tommyy94/Exploring-KL25/Remote/Src/comm.c

#include "comm.h"


/* Local defines */

/* Global variables */
QueueHandle_t xCommQueue;
SemaphoreHandle_t xCommSemaphore;
TaskHandle_t xCommTask = NULL;

struct AMessage
{
    char ucFrame[MAX_FRAME_SIZE];
} xMessage;

    
/* Function descriptions */

/**
 * @brief   FreeRTOS communication task.
 * 
 * @param   pvParam     Unused.
 * 
 * @return  None
 */
void vCommTask(void *const pvParam)
{
    (void)pvParam;
    BaseType_t xAssert;
    struct AMessage *pxMessage;
    const TickType_t xTicksToWait = 100 / portTICK_PERIOD_MS;
    
    for (;;)
    {
        if (xQueueReceive(xCommQueue, &(pxMessage), (TickType_t) 10))
        {
            /* Guard nRF24L01 */
            if (xSemaphoreTake(xCommSemaphore, (TickType_t)xTicksToWait))
            {
                nRF24L01_vSendPayload(pxMessage->ucFrame, strlen(pxMessage->ucFrame));

                /* This call should not fail in any circumstance */
                xAssert = xSemaphoreGive(xCommSemaphore);
                configASSERT(xAssert == pdTRUE);
            }
        }
        
        vTaskDelay(pdMS_TO_TICKS(50));
    }
}


/**
 * @brief   FreeRTOS frame task. Builds the message to send.
 * 
 * @param   pvParam     Unused.
 * 
 * @return  None
 */
void vFrameTask(void *const pvParam)
{
    (void)pvParam;
    int32_t lBytesWritten;
    BaseType_t xAssert;
    
    struct Sensor *pxSensor;
    struct AMessage *pxMessage;
    pxMessage = &xMessage;
    
    for (;;)
    {
        if (xAnalogQueue != 0)
        {
            if (xQueueReceive(xAnalogQueue, &pxSensor, (TickType_t)50))
            {
                /* Build the frame */
                lBytesWritten = csnprintf(pxMessage->ucFrame, MAX_FRAME_SIZE, "tmp=%ldhum=%lumst=%lu", pxSensor->lTemperature, pxSensor->ulHumidity, pxSensor->ulSoilMoisture);
                configASSERT(lBytesWritten >= 0);
            
                /* Transmit */
                xAssert = xQueueSend(xCommQueue, (void *)&pxMessage, (TickType_t)10);
                configASSERT(xAssert);
            }
        }
        
        vTaskDelay(pdMS_TO_TICKS(100));
    }
}


/**
 * @brief   Sets SPI1 SS line high and stops DMA0.
 * 
 * @param   None
 * 
 * @return  None
 */
void TPM2_IRQHandler(void)
{
    BaseType_t xHigherPriorityTaskWoken = pdFALSE;
    
    if (BME_UBFX32(&TPM2->STATUS, TPM_STATUS_TOF_SHIFT, TPM_STATUS_TOF_WIDTH))
    {
        /* Cleanup */
        SPI1_vSetSlave(HIGH);
        TPM2_vStop();

        /* Should not be NULL as transmission was in progress */
        configASSERT(xCommTask != NULL);

        /* Notify task */
        vTaskNotifyGiveFromISR(xCommTask, &xHigherPriorityTaskWoken);
        
        /* Transmission no longer in progress */
        xCommTask = NULL;
    }

    /* Clear Timer Overflow Flag */
    BME_OR32(&TPM2->STATUS, TPM_STATUS_TOF(1));

    /* Force context switch if xHigherPriorityTaskWoken is set pdTRUE */
    portEND_SWITCHING_ISR(xHigherPriorityTaskWoken);
}
