tommyy94/Exploring-KL25/Remote/Inc/includes.h

#pragma once

#include <stdlib.h>
#include <string.h>

#include "MKL25Z4.h"

#include "defines.h"
#include "printf-stdarg.h"
#include "system.h"
#include "motor.h"
#include "comm.h"
#include "sensors.h"
#include "adc.h"
#include "dma.h"
#include "tpm.h"
#include "spi.h"
#include "HS1101.h"
#include "nrf24l01.h"
