tommyy94/Exploring-KL25/Remote/Src/HS1101.c

/* User headers */
#include  "HS1101.h"

/* Local defines */
#define HUMIDITY_FORMULA(x) ((x))

/* Local variables */
TaskHandle_t xAnalogNotification = NULL;

/* Local function prototypes */
static void HS1101_vSendSignal(void);


/* Function descriptions */

/**
 * @brief   This function simply sets ports output & writes high to memory so
 *          multiplexing pins sets pin high.
 * 
 * @param   None
 * 
 * @return  None
 */
void HS1101_vInit(void)
{
    FGPIOE->PDDR |= MASK(HUMID_SENSOR_PIN);
    FGPIOE->PSOR |= MASK(HUMID_SENSOR_PIN);
}


/**
 * @brief   Start measuring HS1101 capacitance using CMP0 and TPM0 Input Capture mode.
 *          This function disables context switches for few cycles, because timer and
 *          comparator must be started at the same time.
 * 
 * @param   None
 * 
 * @return  None
 */
static void HS1101_vSendSignal(void)
{    
    /* Charge capacitor */
    BME_OR32(&PORTE->PCR[HUMID_SENSOR_PIN], PORT_PCR_MUX(ALT1));
    
    /* Start atomic operations */
    taskENTER_CRITICAL();
    
    /* Start timer */
    BME_OR32(&TPM1->SC, TPM_SC_CMOD(1));
    
    /* Set IO to inverted comparator mode */
    BME_BFI32(&PORTE->PCR[HUMID_SENSOR_PIN], ALT0 << PORT_PCR_MUX_SHIFT, PORT_PCR_MUX_SHIFT, 1);
    
    /* Stop atomic operations */
    taskEXIT_CRITICAL();
}


/**
 * @brief   Read variable capacitor HS1101 using CMP0 and TMP0.
 * 
 * @param   None
 * 
 * @return  ulHumid     Air humidity value.
 * 
 * @todo    Calibrate humidity sensor
 */
uint32_t HS1101_ulReadHumidity(void)
{
    BaseType_t xAssert;
    const TickType_t xTicksToWait = 100 / portTICK_PERIOD_MS;
    uint32_t HS1101_ulValue = 0;
    uint32_t ulHumid = 0;
    
    /* No conversion should be in progress */
    configASSERT(xAnalogNotification == NULL);
    
    /* Update status */
    xAnalogNotification = xTaskGetCurrentTaskHandle();
    
    /* Start conversion */
    HS1101_vSendSignal();
    
    /* Wait until conversion done */
    xAssert = xTaskNotifyWait(0x00, 0xFFFFFFFF, &HS1101_ulValue, xTicksToWait);
    configASSERT(xAssert == pdPASS);
    
    /* Convert analog value and return it */
    ulHumid = HUMIDITY_FORMULA(HS1101_ulValue);
    return (ulHumid);
}
