tommyy94/Exploring-KL25/kl25_test/Src/gpio.c

#include "gpio.h"


/* Function descriptions */

/**
 * @brief   Mainly used for debugging purposes.
 * 
 * @param   None
 * 
 * @return  None
 */
void GPIO_vInit(void)
{
    /* Enable clock to PORTD */
    SIM->SCGC5 |= SIM_SCGC5_PORTD_MASK;
    
    /* Select GPIO for pin */
    PORTD->PCR[SIGNAL_SHIFT] = PORT_PCR_MUX(ALT1);
    
    /* Set port to output */
    FGPIOD->PDDR |= MASK(SIGNAL_SHIFT);
}
