tommyy94/Exploring-KL25/kl25_test/Inc/gpio.h

/**
 * gpioh.
 * This compilation unit handles GPIO.
 */

#pragma once

/* System headers */
#include <stdint.h>
#include <string.h>

/* Device vendor headers */
#include "MKL25Z4.h"

/* User headers */
#include "defines.h"


/* Global function prototypes */
void GPIO_vInit(void);
